EnAccess/OpenPAYGO-HDK/hardware/OpenPAYGO-HDK.kicad_sch

## KiCad design hardware/OpenPAYGO-HDK.kicad_sch (2024-02-26)

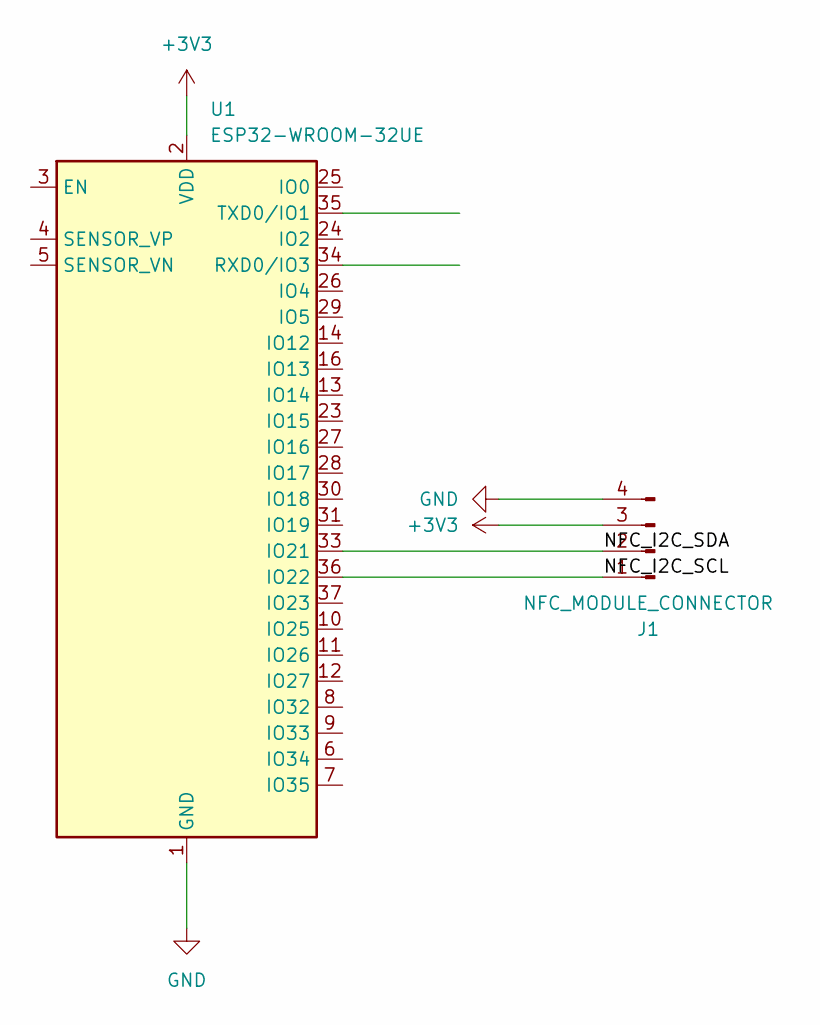
[picture p4: schematic OpenPAYGO-HDK.kicad_sch]

Parts:
J1: NFC_MODULE_CONNECTOR
U1: ESP32-WROOM-32UE

Connections:
+3V3: J1.3, U1.2 (VDD)
GND: J1.4, U1.1 (GND), U1.15 (GND), U1.38 (GND), U1.39 (GND)
NFC_I2C_SCL: J1.1, U1.36 (IO22)
NFC_I2C_SDA: J1.2, U1.33 (IO21)
