EnAccess/OpenPAYGO-HDK/factory_setup.h

#ifndef FACTORY_H
#define FACTORY_H

// Imports
#include <Arduino.h>
#include "hal.h"

// Defines

// Hardware defines

// Functions
void factorySetupLoop();
bool isFactorySetupDone();

// Variables

#endif
